doublehan07/RollingBall/Intro/1.jpg

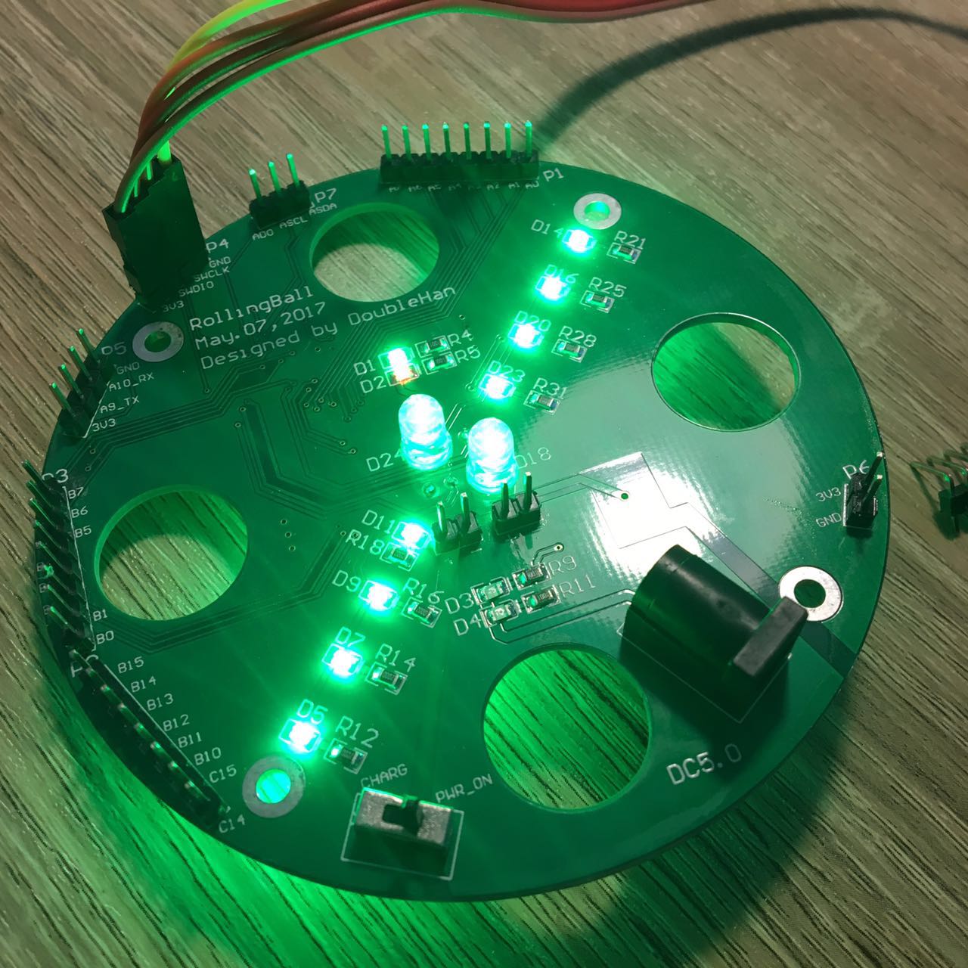
Intro/1.jpg
