doublehan07/RollingBall/Codes/RollingBall/HARDWARE/LED/LED.C

#include "led.h"
/**************************************************************************
函数功能：LED接口初始化
入口参数：无 
返回  值：无
**************************************************************************/
void LED_Init(void)
{
	RCC->APB2ENR|=1<<2; //使能 PORTA 时钟  

	GPIOA->CRH&=0XFFFFFFF0;
	GPIOA->CRH|=0X00000003;//PA8 推挽输出
	GPIOA->ODR|=0<<8; //PA8 输出low
	
	GPIOA->CRH&=0XFFFF0FFF;
	GPIOA->CRH|=0X00003000;//PA11 推挽输出
	GPIOA->ODR|=0<<11; //PA11 输出low
	
		
	GPIOA->CRH&=0XFFF0FFFF;
	GPIOA->CRH|=0X00030000;//PA12 推挽输出
	GPIOA->ODR|=0<<12; //PA12 输出low
	
		
	GPIOA->CRH&=0X0FFFFFFF;
	GPIOA->CRH|=0X30000000;//PA15 推挽输出
	GPIOA->ODR|=0<<15; //PA15 输出low
	
	RCC->APB2ENR|=1<<4; //使能 PORTC 时钟  
	
	GPIOC->CRH&=0XFF0FFFFF;
	GPIOC->CRH|=0X00300000;//PC13 推挽输出
	GPIOC->ODR|=0<<13; //PC13 输出low
}
